Elecrow-RD/CrowPanel-Advance-7.0-HMI-ESP32-AI-Display-800x480/example/example_code7.0/lesson-08/README.md

# **A simple AI text generation text exchange example**

This case illustrates generating text through the connection between the Advanced AI screen and the NVIDIA Large Model API.

***\*Note: All examples run on ESP32 version 3.0.2.\****

### **How to use example**

First, learn how to obtain the Nvidia model key, and then replace it in the code.After opening the sample code in the relevant code file with Arduino IDE.set the required configuration parameters and program it onto the development board

***\*Configuration parameter：\****

图片8-1

### **How to add Arduino libraries**

Replace the libraries file with the following path:

C:\Users\user name\Documents\Arduio\libraries

***\*Note\****: The 'user name' here is the same as the user computer account name.

## **Documentation tutorial link**：

https://www.elecrow.com/pub/wiki/4.3_8_Elementary_chatbot.html

## **Video** **tutorial link**：

https://www.youtube.com/watch?v=JtD7eXJt2Zk&list=PLwh4PlcPx2Gfrtm7TmlARyF4ccTmIy-gK&index=7&t=1s
