Elecrow-RD/CrowPanel-Advance-7.0-HMI-ESP32-AI-Display-800x480/example/example_code7.0/lesson-09/Wireless Modular Burn Board/readme.md

### Wirless Module H2/C6 Special board burning mode

##### 1.Gather the necessary tools

| | tools | quantity |
| ---- | --- | --- |
| 1 | Wirless Module H2/C6 | 1 |
| 2 | wirless Module_testboard | 1 |

 

Wirless Module H2/C6



wirless Module_testboard

##### 2.wiring

Wirless Module H2/C6 Insert in the direction of the arrow.

 

##### 3.Burning

Connect the serial module to the computer and find the corresponding serial device number (e.g. COM35) in the Task Manager.

 

Open Arduino or open the corresponding serial port under any serial port tool.



Press and hold the BOOT key and then press the RST key to enter burn mode.



The serial monitor prints to enter burn-in mode.
