Elecrow-RD/CrowPanel-Advance-7.0-HMI-ESP32-AI-Display-800x480/example/example_code7.0/Advance_AIchat/10-1.png

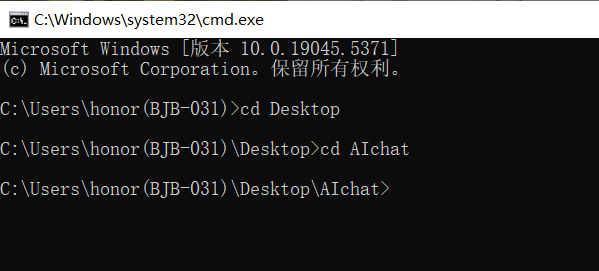
example/example_code7.0/Advance_AIchat/10-1.png
