Elecrow-RD/CrowPanel-Advance-7.0-HMI-ESP32-AI-Display-800x480/example/example_code7.0/lesson-10/Thread/ot_cli/main/esp_ot_cli.c

/*
 * SPDX-FileCopyrightText: 2021-2024 Espressif Systems (Shanghai) CO LTD
 *
 * SPDX-License-Identifier: CC0-1.0
 *
 * OpenThread Command Line Example
 *
 * This example code is in the Public Domain (or CC0 licensed, at your option.)
 *
 * Unless required by applicable law or agreed to in writing, this
 * software is distributed on an "AS IS" BASIS, WITHOUT WARRANTIES OR
 * CONDITIONS OF ANY KIND, either express or implied.
*/

#include <stdio.h>
#include <unistd.h>
#include <string.h>

#include "sdkconfig.h"
#include "esp_err.h"
#include "esp_event.h"
#include "esp_log.h"
#include "esp_netif.h"
#include "esp_netif_types.h"
#include "esp_openthread.h"
#include "esp_openthread_cli.h"
#include "esp_openthread_lock.h"
#include "esp_openthread_netif_glue.h"
#include "esp_openthread_types.h"
#include "esp_ot_config.h"
#include "esp_vfs_eventfd.h"
#include "driver/uart.h"
#include "freertos/FreeRTOS.h"
#include "freertos/task.h"
#include "hal/uart_types.h"
#include "nvs_flash.h"
#include "openthread/cli.h"
#include "openthread/instance.h"
#include "openthread/logging.h"
#include "openthread/tasklet.h"

#if CONFIG_OPENTHREAD_STATE_INDICATOR_ENABLE
#include "ot_led_strip.h"
#endif

#if CONFIG_OPENTHREAD_CLI_ESP_EXTENSION
#include "esp_ot_cli_extension.h"
#endif // CONFIG_OPENTHREAD_CLI_ESP_EXTENSION

#define TAG "ot_esp_cli"

static esp_netif_t *init_openthread_netif(const esp_openthread_platform_config_t *config)
{
    esp_netif_config_t cfg = ESP_NETIF_DEFAULT_OPENTHREAD();
    esp_netif_t *netif = esp_netif_new(&cfg);
    assert(netif != NULL);
    ESP_ERROR_CHECK(esp_netif_attach(netif, esp_openthread_netif_glue_init(config)));

    return netif;
}

static void ot_task_worker(void *aContext)
{
    esp_openthread_platform_config_t config = {
        // .radio_config = ESP_OPENTHREAD_DEFAULT_RADIO_CONFIG(),
        .radio_config = {                                                      
            .radio_mode = RADIO_MODE_NATIVE,//Use the native 15.4 radio                  
        },
        // .host_config = ESP_OPENTHREAD_DEFAULT_HOST_CONFIG(),//CLI UART connection to the host
        .host_config = {
            .host_connection_mode = HOST_CONNECTION_MODE_CLI_UART,  
            .host_uart_config = {                                   
                .port = 0,                                          
                .uart_config =                                      
                    {                                               
                        .baud_rate = 115200,                        
                        .data_bits = UART_DATA_8_BITS,              
                        .parity = UART_PARITY_DISABLE,              
                        .stop_bits = UART_STOP_BITS_1,              
                        .flow_ctrl = UART_HW_FLOWCTRL_DISABLE,      
                        .rx_flow_ctrl_thresh = 0,                   
                        .source_clk = UART_SCLK_DEFAULT,            
                    },                                              
                .rx_pin = UART_PIN_NO_CHANGE,                       
                .tx_pin = UART_PIN_NO_CHANGE,                       
            }, //connet mode -- Uart Pin 11 12
        },
        .port_config = ESP_OPENTHREAD_DEFAULT_PORT_CONFIG(),//The partition for storing OpenThread dataset  
    };


    ESP_ERROR_CHECK(esp_openthread_init(&config));// Initialize the OpenThread stack

#if CONFIG_OPENTHREAD_STATE_INDICATOR_ENABLE
    ESP_ERROR_CHECK(esp_openthread_state_indicator_init(esp_openthread_get_instance()));
#endif
    esp_openthread_lock_acquire(portMAX_DELAY);//Openthread api lock
#if CONFIG_OPENTHREAD_LOG_LEVEL_DYNAMIC
    // The OpenThread log level directly matches ESP log level
    (void)otLoggingSetLevel(CONFIG_LOG_DEFAULT_LEVEL);
#endif
    // Initialize the OpenThread cli
#if CONFIG_OPENTHREAD_CLI
    esp_openthread_cli_init();
#endif

    esp_netif_t *openthread_netif;
    // Initialize the esp_netif bindings
    openthread_netif = init_openthread_netif(&config);//Creates an instance of new esp-netif object based on provided config,attach the processing program to the network interface(
    esp_netif_set_default_netif(openthread_netif);

#if CONFIG_OPENTHREAD_CLI_ESP_EXTENSION
    esp_cli_custom_command_init();
#endif // CONFIG_OPENTHREAD_CLI_ESP_EXTENSION

    // Run the main loop
#if CONFIG_OPENTHREAD_CLI
    esp_openthread_cli_create_task();
#endif
#if CONFIG_OPENTHREAD_AUTO_START
    otOperationalDatasetTlvs dataset;
    otError error = otDatasetGetActiveTlvs(esp_openthread_get_instance(), &dataset);
    ESP_ERROR_CHECK(esp_openthread_auto_start((error == OT_ERROR_NONE) ? &dataset : NULL));
#endif
    esp_openthread_lock_release();//Openthread api lock release 
    esp_openthread_launch_mainloop();//Launches the OpenThread main loop.

    // Clean up
    esp_openthread_netif_glue_deinit();
    esp_netif_destroy(openthread_netif);

    esp_vfs_eventfd_unregister();
    vTaskDelete(NULL);
}

void app_main(void)
{
    // Used eventfds:
    // * netif
    // * ot task queue
    // * radio driver
    esp_vfs_eventfd_config_t eventfd_config = {
        .max_fds = 3,
    };

    ESP_ERROR_CHECK(nvs_flash_init());//nvs partition init
    ESP_ERROR_CHECK(esp_event_loop_create_default());//create default loop event
    ESP_ERROR_CHECK(esp_netif_init());//init tcp/ip stack
    ESP_ERROR_CHECK(esp_vfs_eventfd_register(&eventfd_config));//Registers the event vfs(Used for implementing task notifications in the OpenThread protocol stack)
    xTaskCreate(ot_task_worker, "ot_cli_main", 10240, xTaskGetCurrentTaskHandle(), 5, NULL);
}
